s7appo/ELEMENT-camping-platform/images/8607A12A-2D4D-4090-AF0A-3B770DCC6D59.jpg

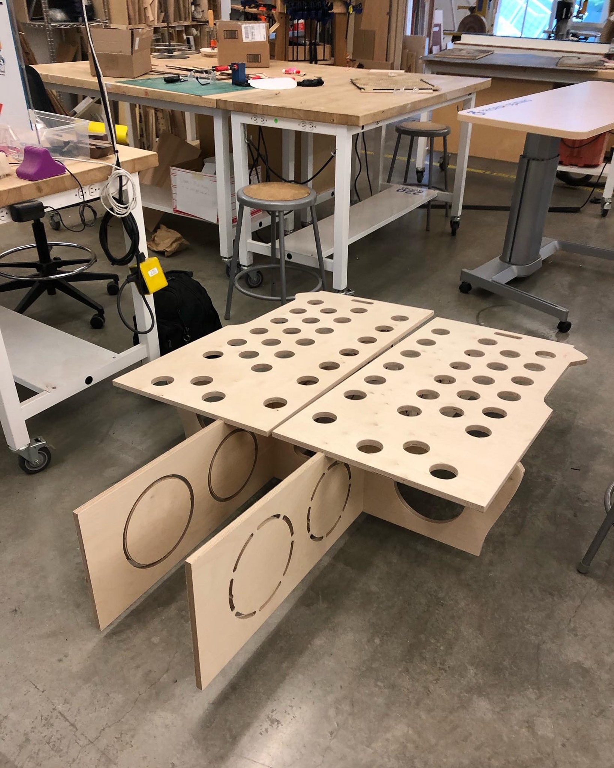
images/8607A12A-2D4D-4090-AF0A-3B770DCC6D59.jpg
