s7appo/ELEMENT-camping-platform/images/IMG_0168.jpg

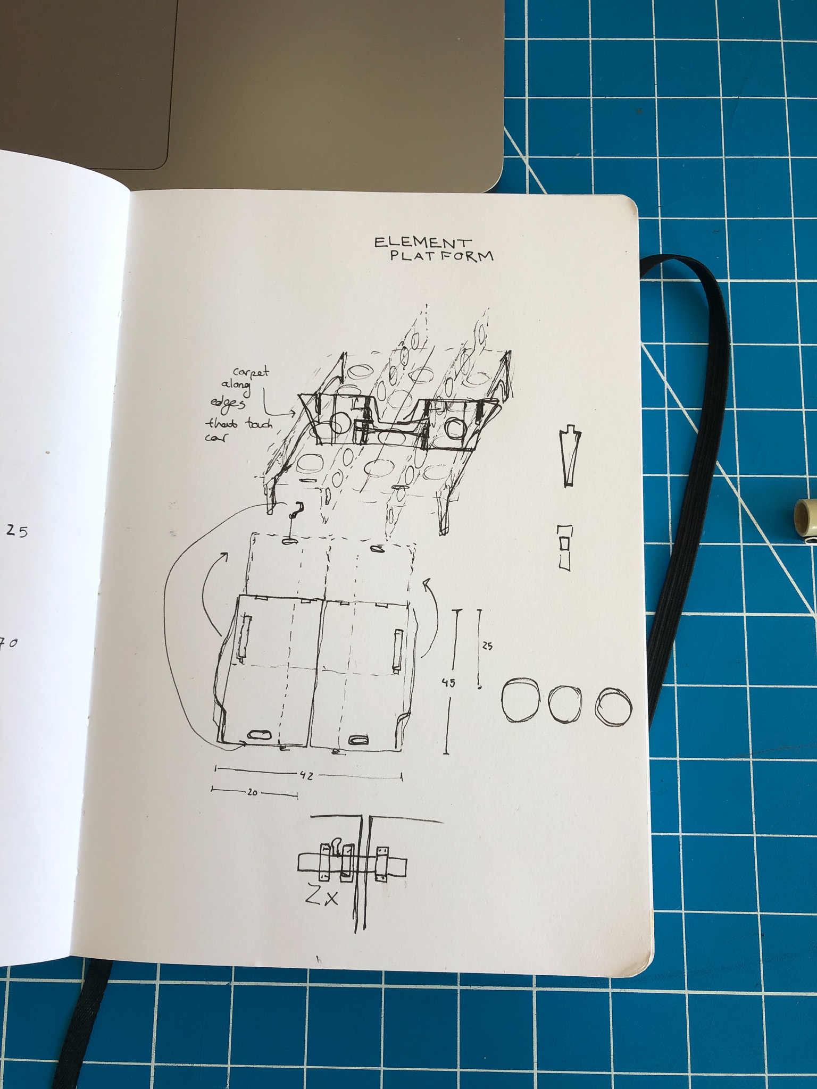
images/IMG_0168.jpg
