s7appo/ELEMENT-camping-platform/images/IMG_0304.jpg

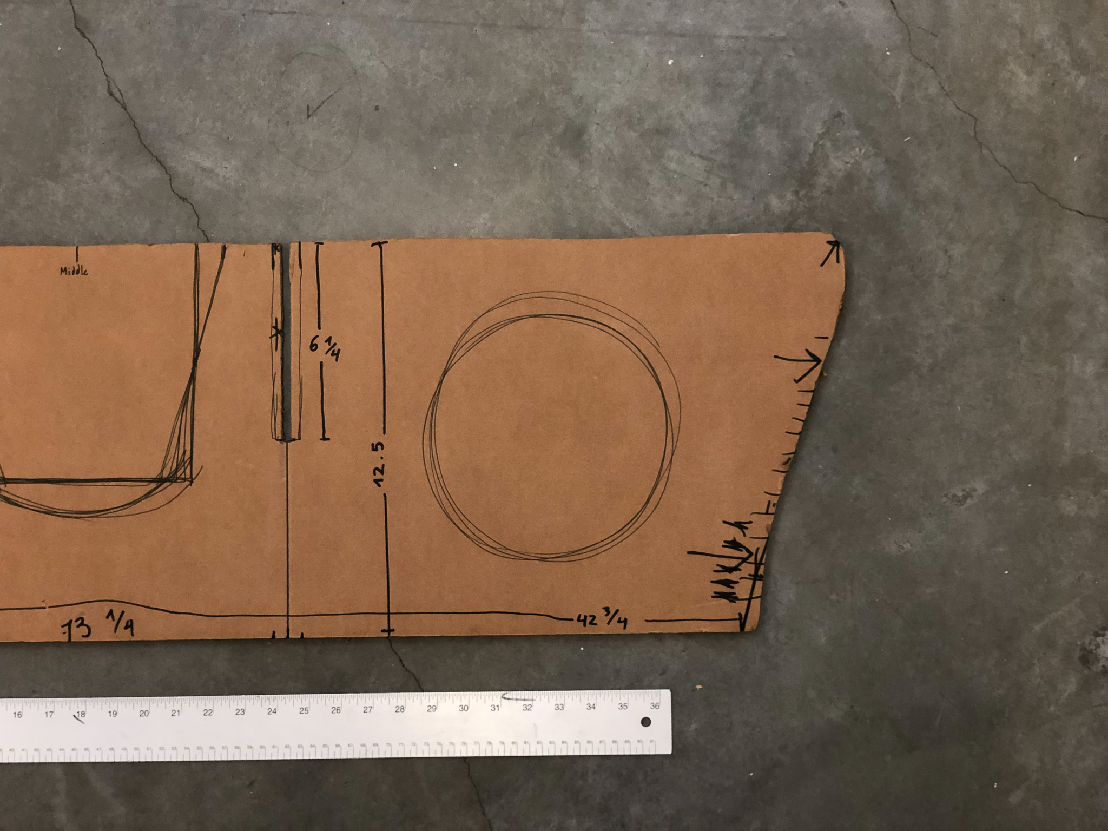
images/IMG_0304.jpg
