s7appo/ELEMENT-camping-platform/images/IMG_1578.jpg

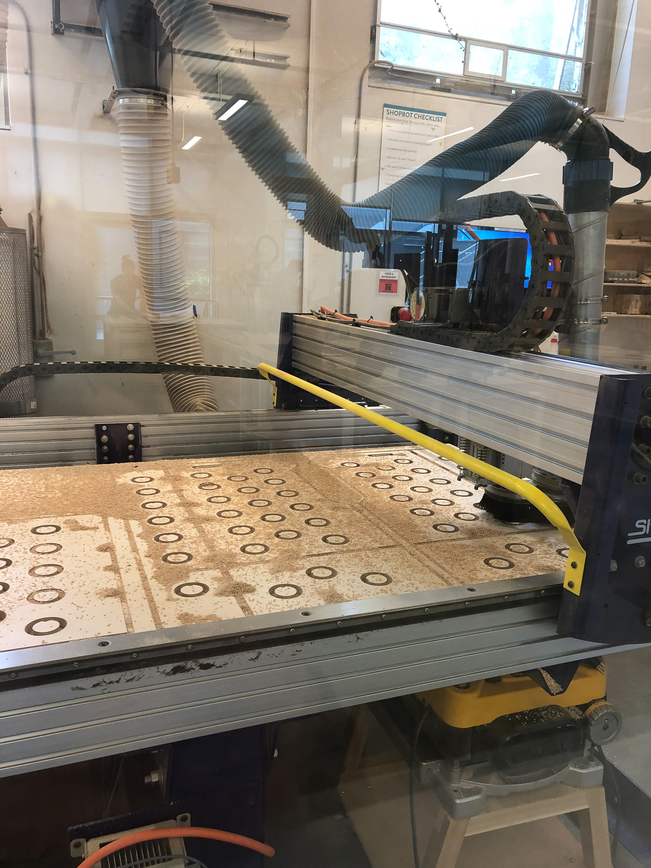
images/IMG_1578.jpg
