s7appo/ELEMENT-camping-platform/images/IMG_1602.jpg

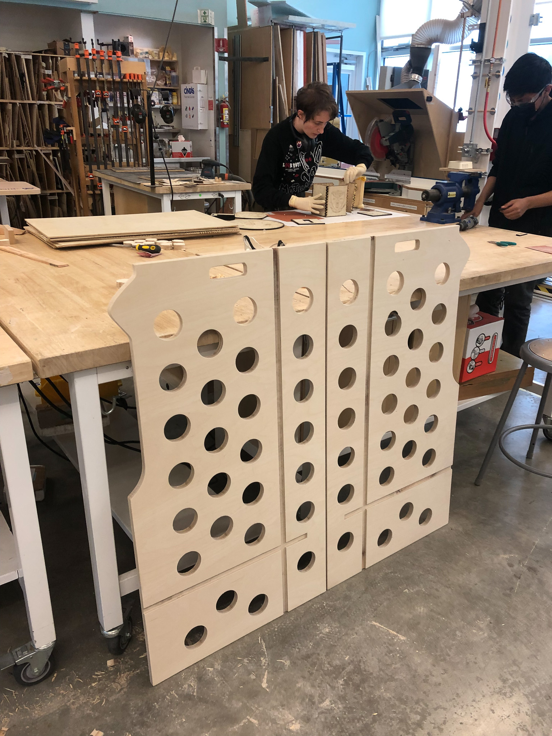
images/IMG_1602.jpg
