s7appo/ELEMENT-camping-platform/images/IMG_1611.jpg

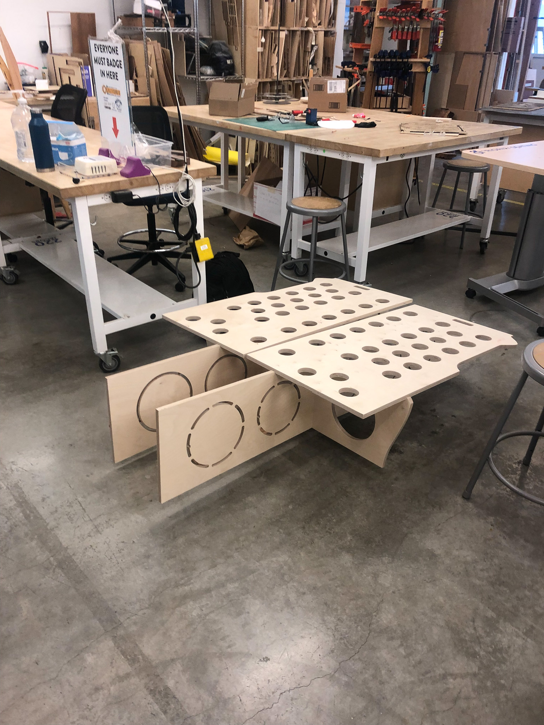
images/IMG_1611.jpg
