s7appo/ELEMENT-camping-platform/images/IMG_1734.jpg

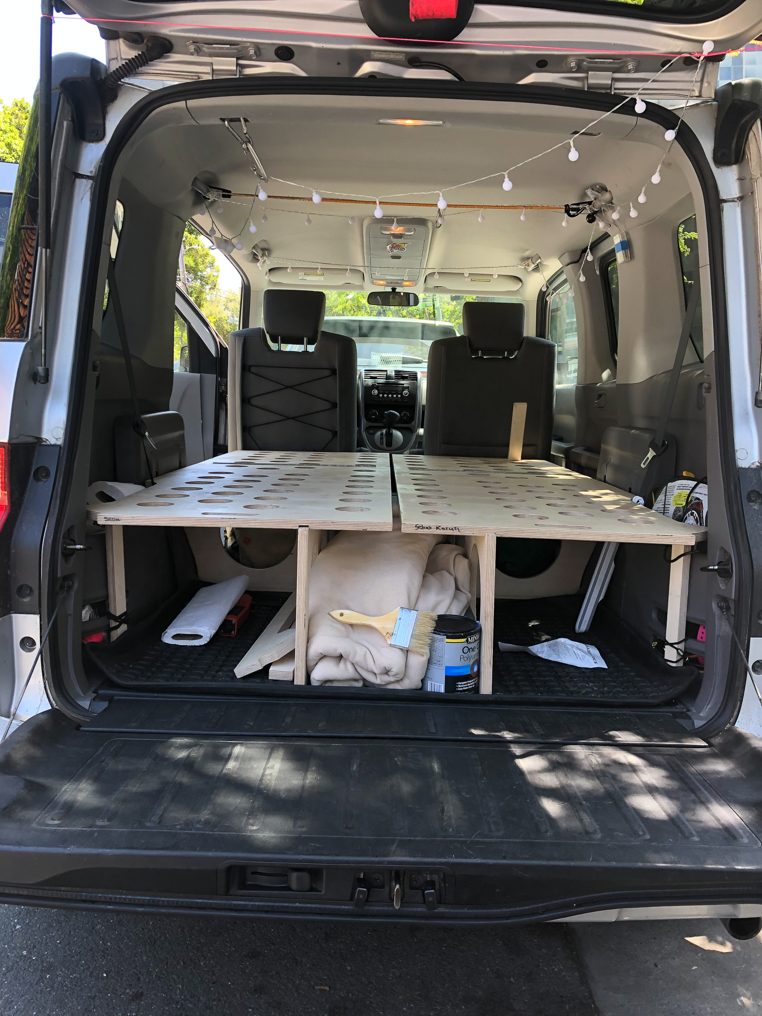
images/IMG_1734.jpg
