s7appo/ELEMENT-camping-platform/images/IMG_1735.jpg

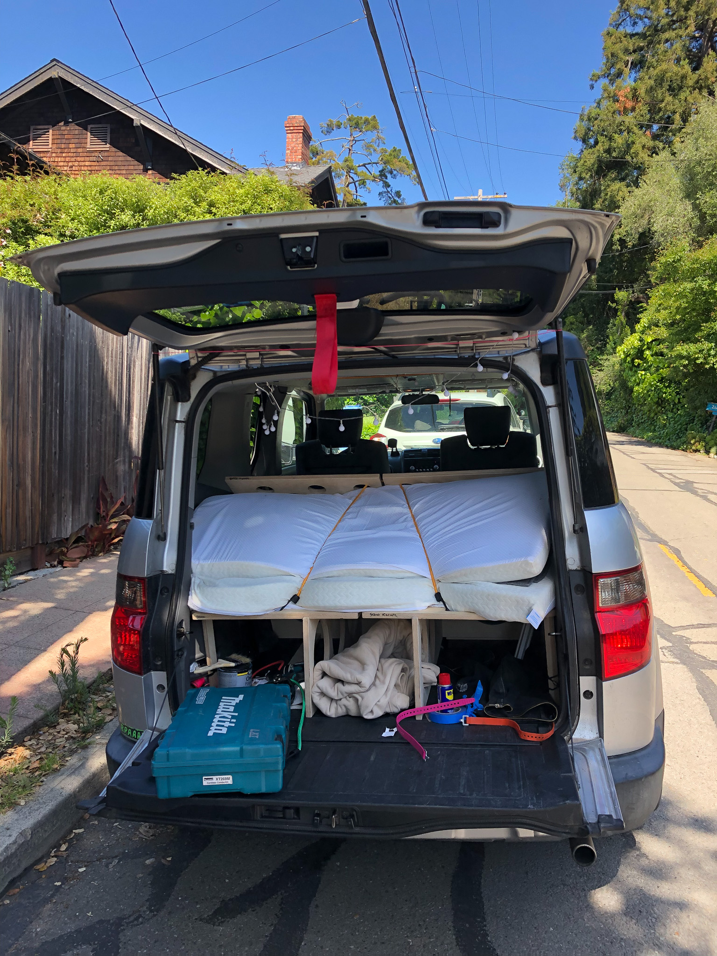
images/IMG_1735.jpg
