s7appo/ELEMENT-camping-platform/images/IMG_1738.jpg

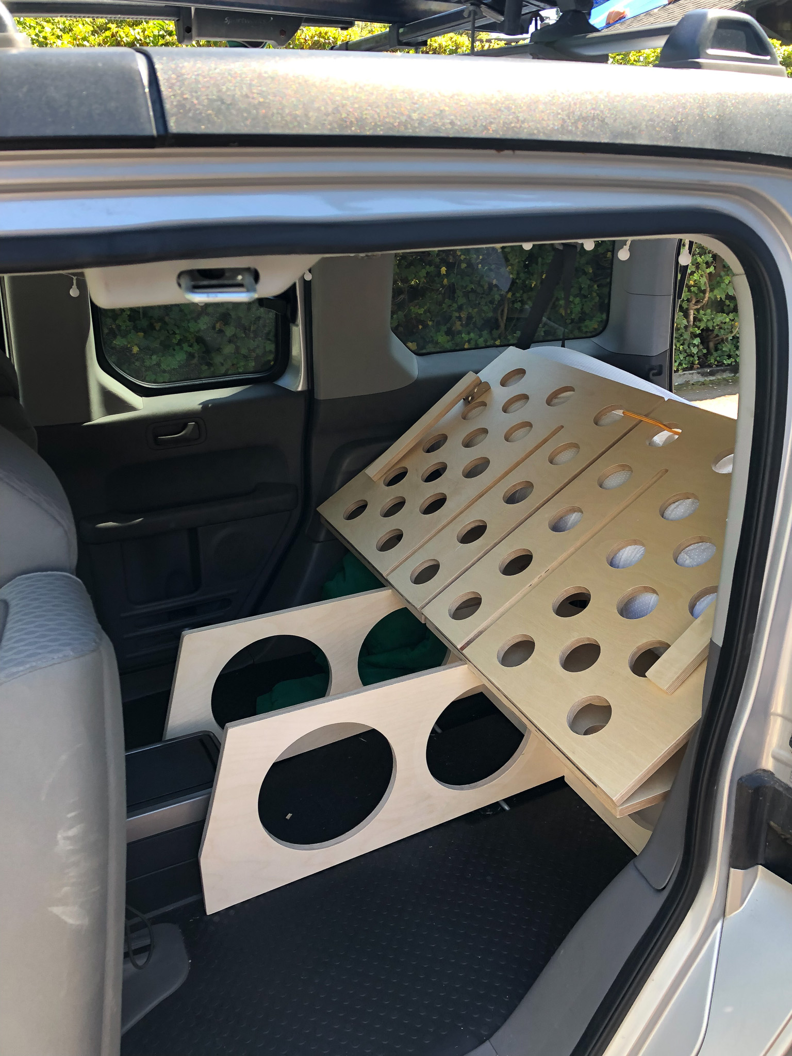
images/IMG_1738.jpg
