s7appo/ELEMENT-camping-platform/images/IMG_1740.jpg

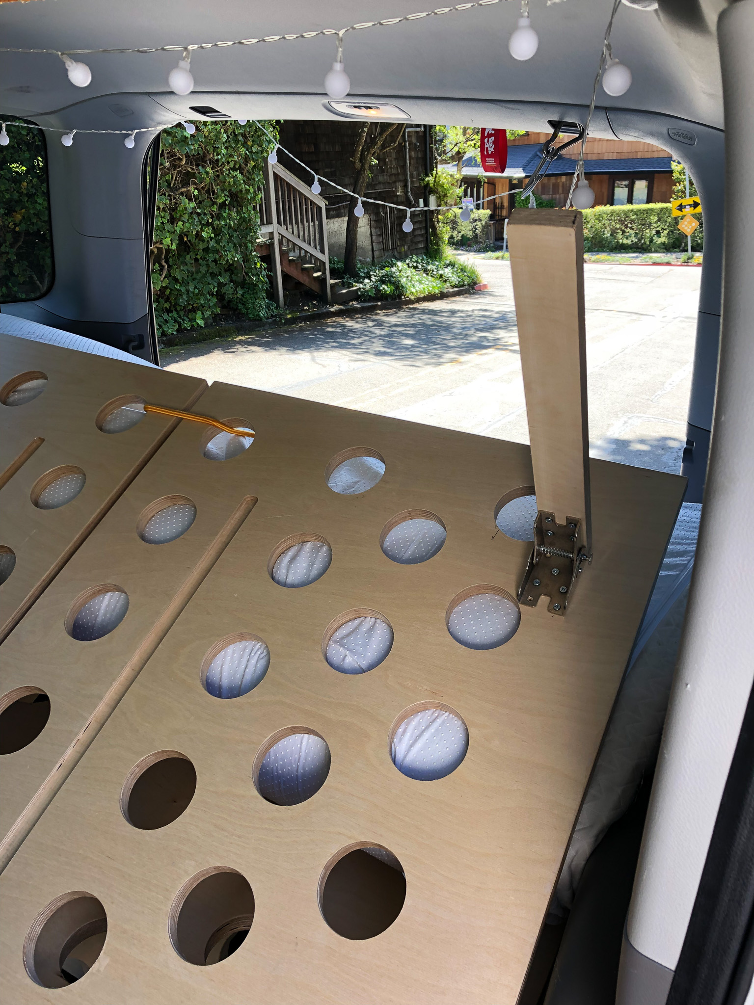
images/IMG_1740.jpg
