s7appo/ELEMENT-camping-platform/images/IMG_1876.jpg

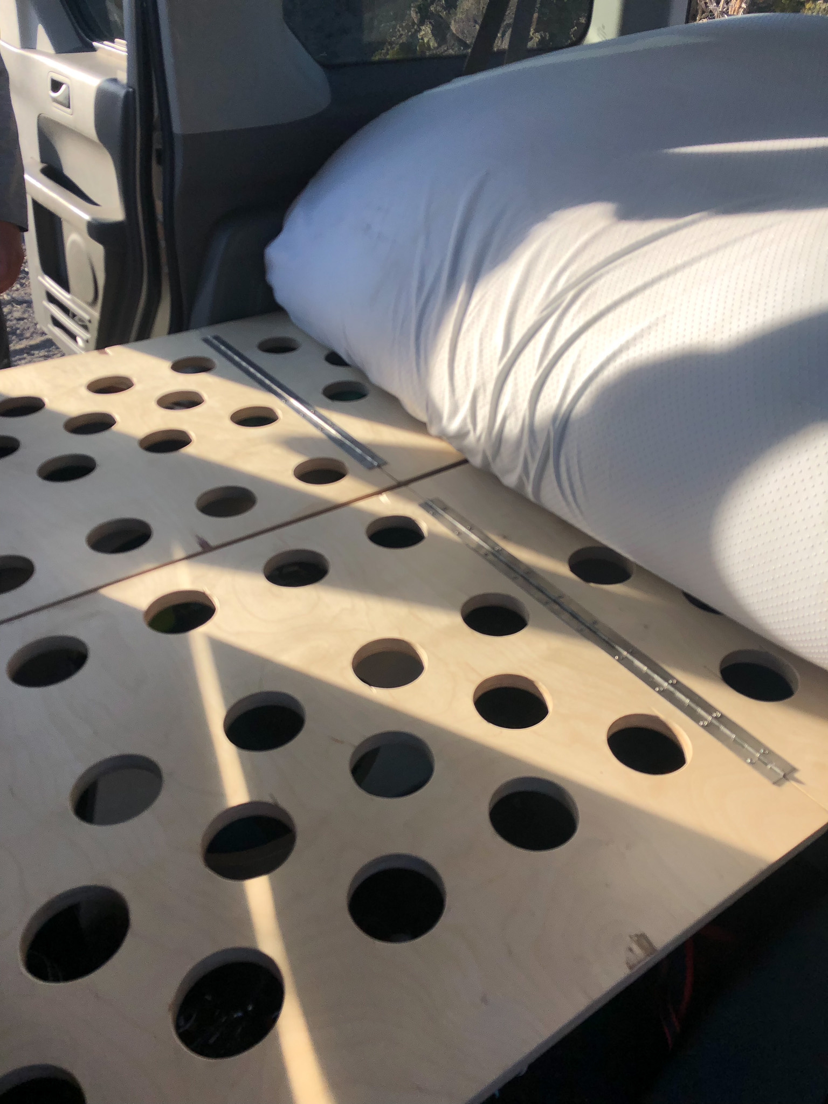
images/IMG_1876.jpg
