s7appo/ELEMENT-camping-platform/images/IMG_1924.jpg

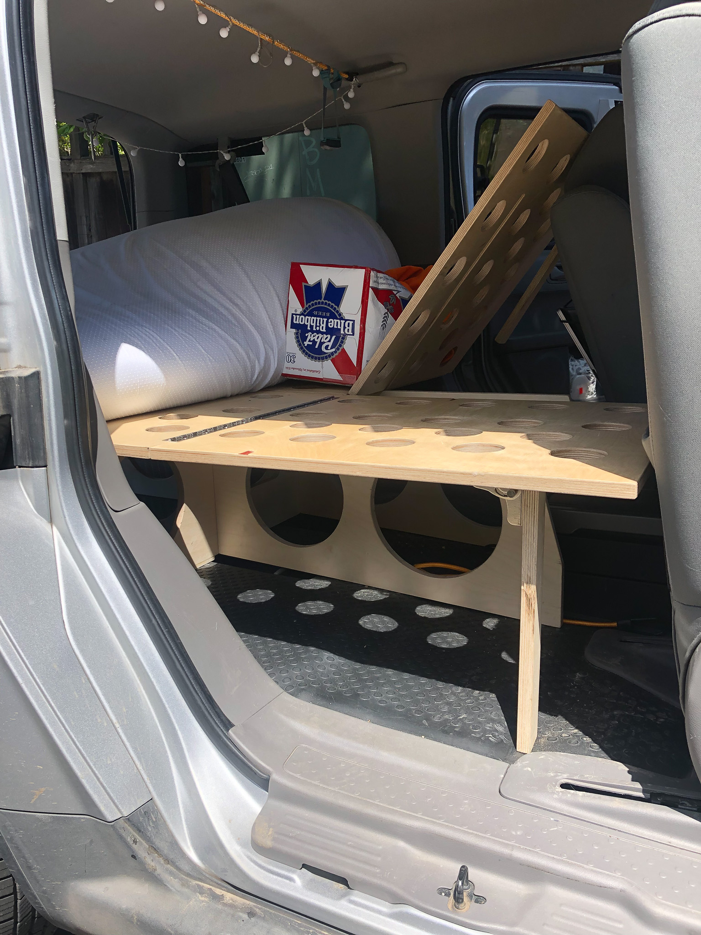
images/IMG_1924.jpg
