s7appo/ELEMENT-camping-platform/images/IMG_7135.jpg

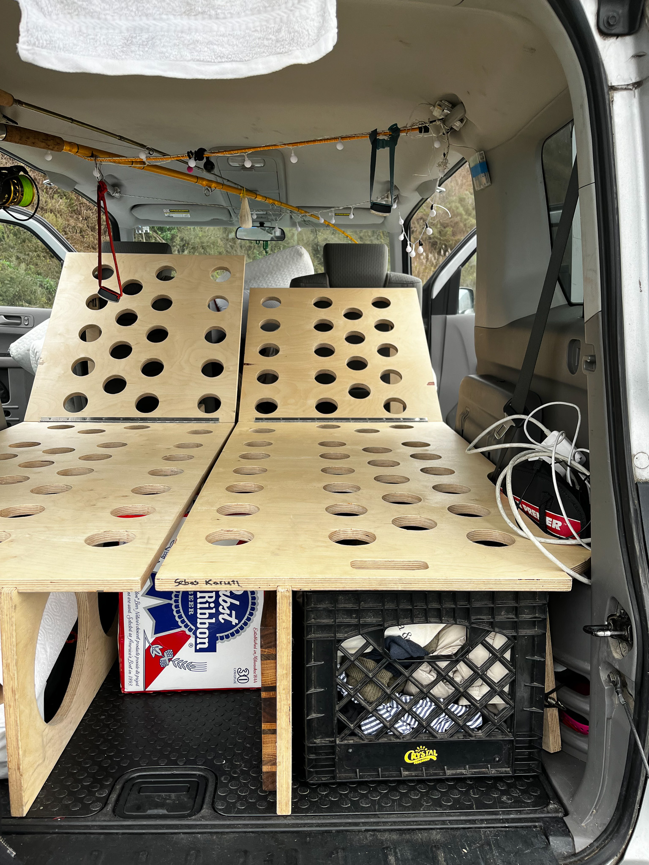
images/IMG_7135.jpg
