s7appo/ELEMENT-camping-platform/images/IMG_7140.jpg

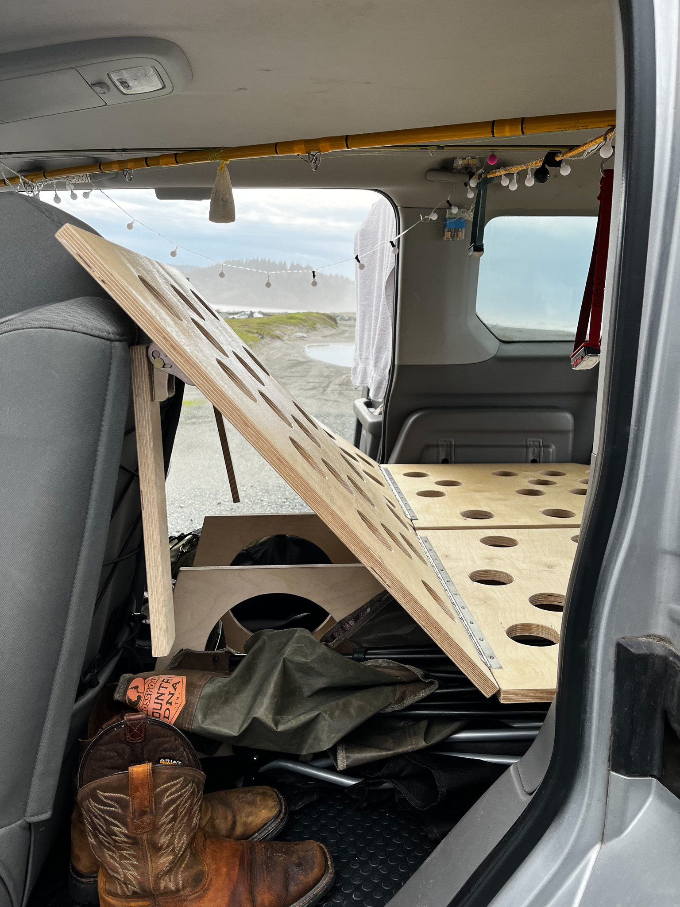
images/IMG_7140.jpg
