s7appo/ELEMENT-camping-platform/images/IMG_7141.jpg

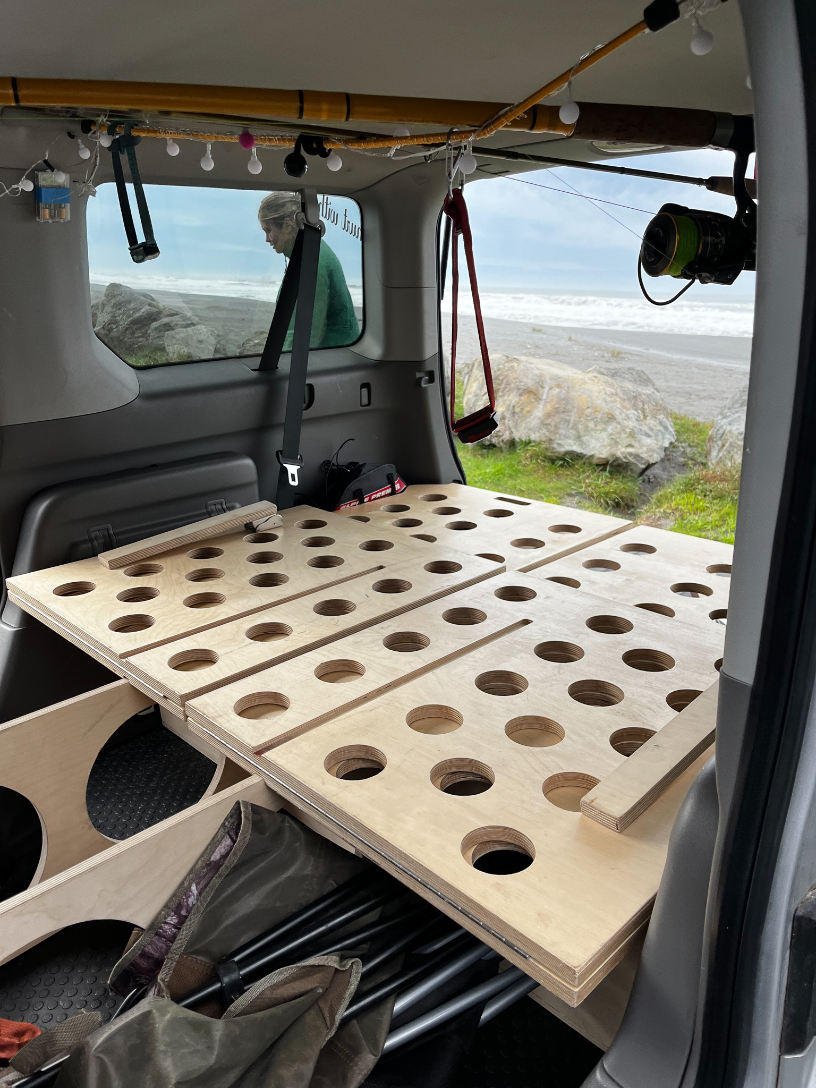
images/IMG_7141.jpg
