s7appo/ELEMENT-camping-platform/images/IMG_7143.jpg

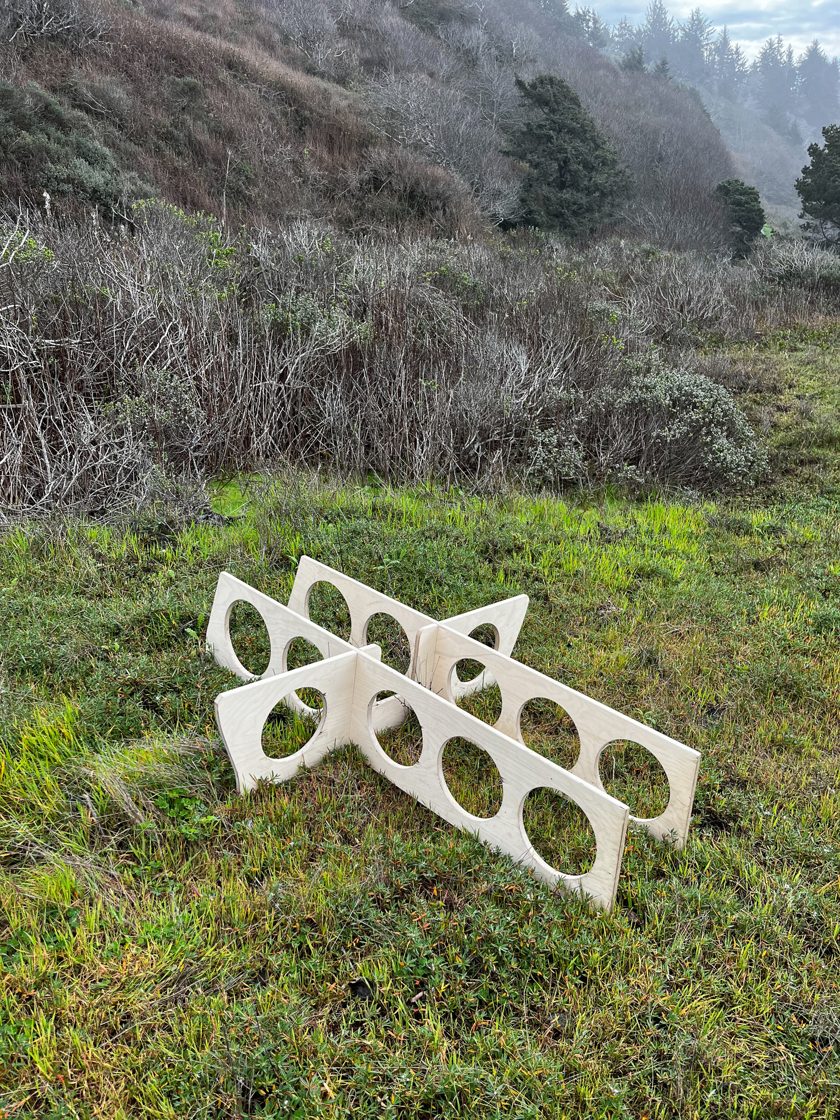
images/IMG_7143.jpg
