s7appo/ELEMENT-camping-platform/images/IMG_7145.jpg

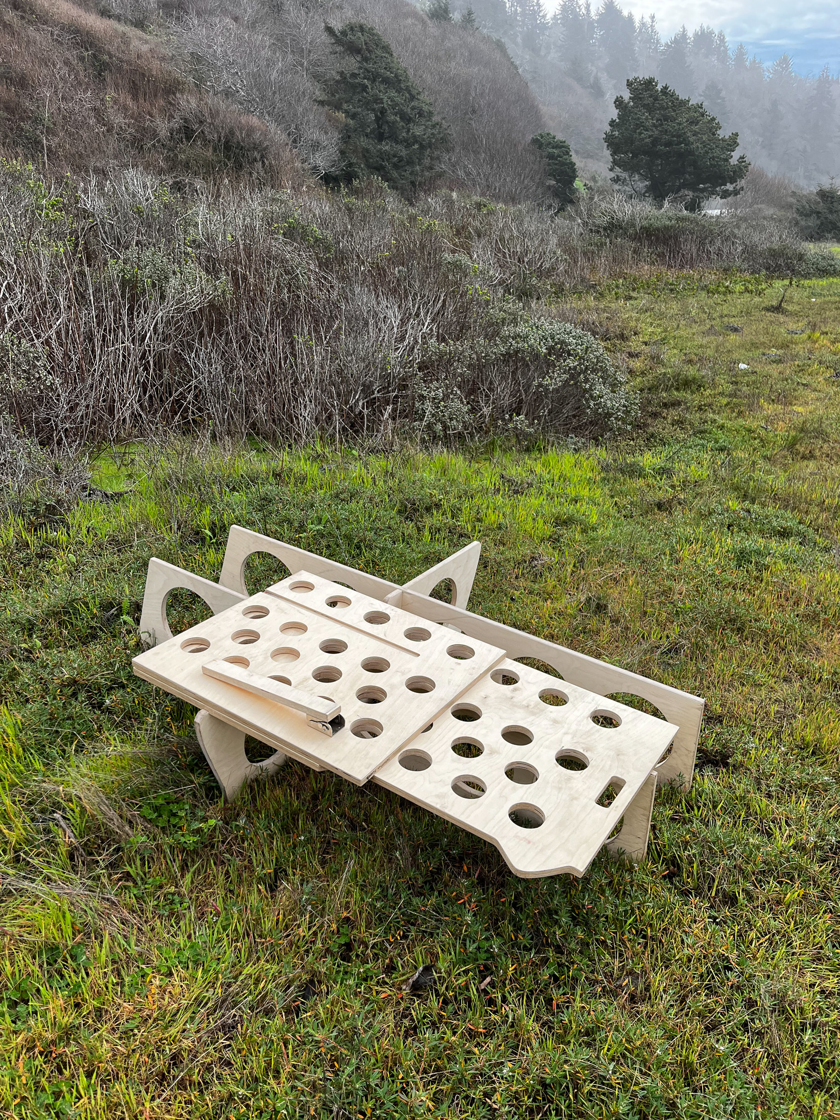
images/IMG_7145.jpg
