s7appo/ELEMENT-camping-platform/images/IMG_7146.jpg

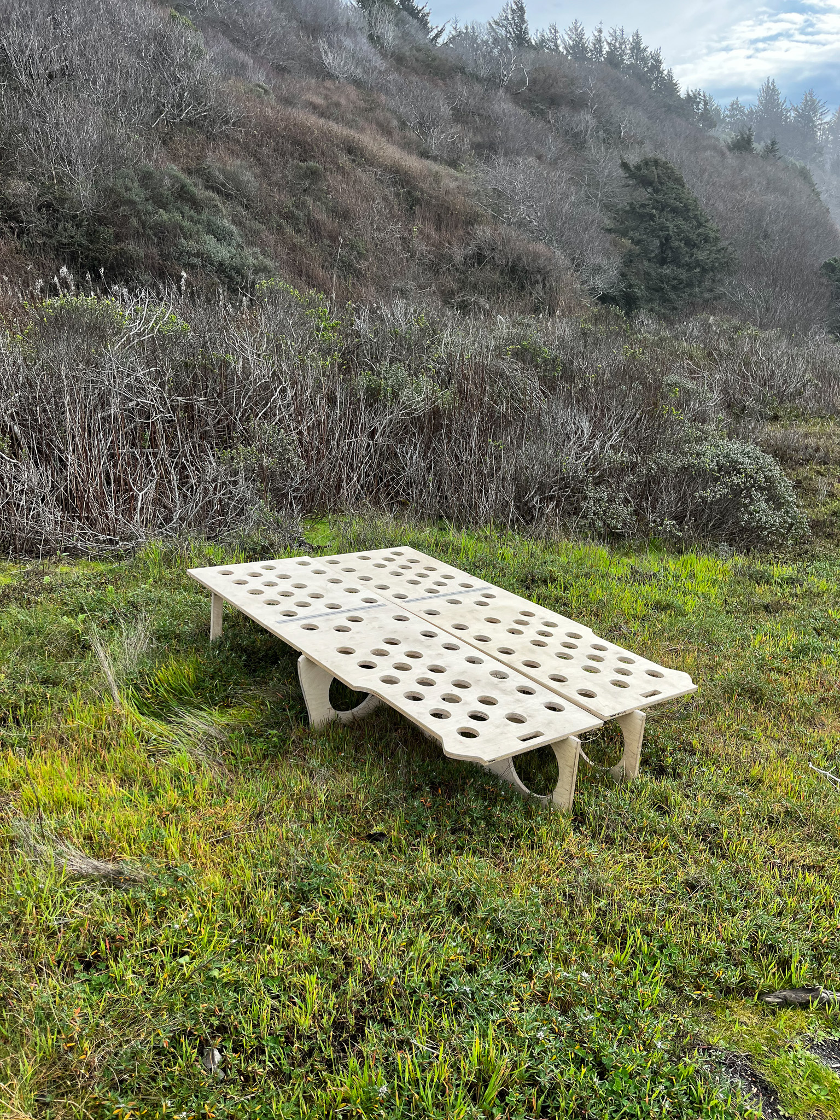
images/IMG_7146.jpg
