s7appo/ELEMENT-camping-platform/images/IMG_7158.jpg

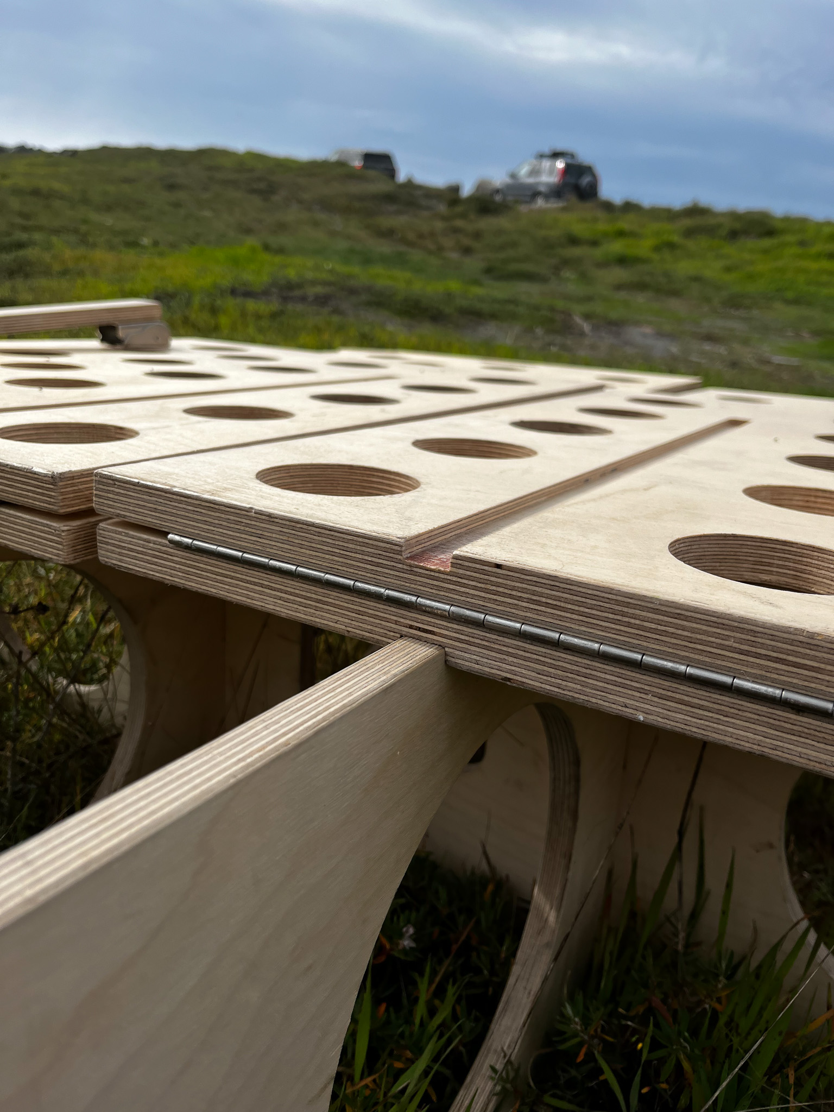
images/IMG_7158.jpg
