s7appo/ELEMENT-camping-platform/images/IMG_7159.jpg

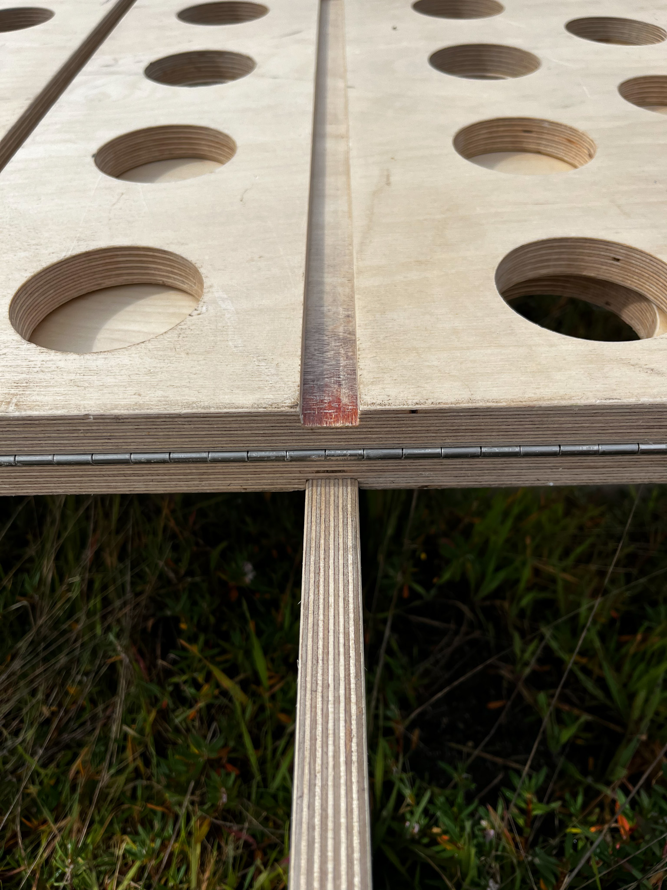
images/IMG_7159.jpg
