s7appo/ELEMENT-camping-platform/images/IMG_7160.jpg

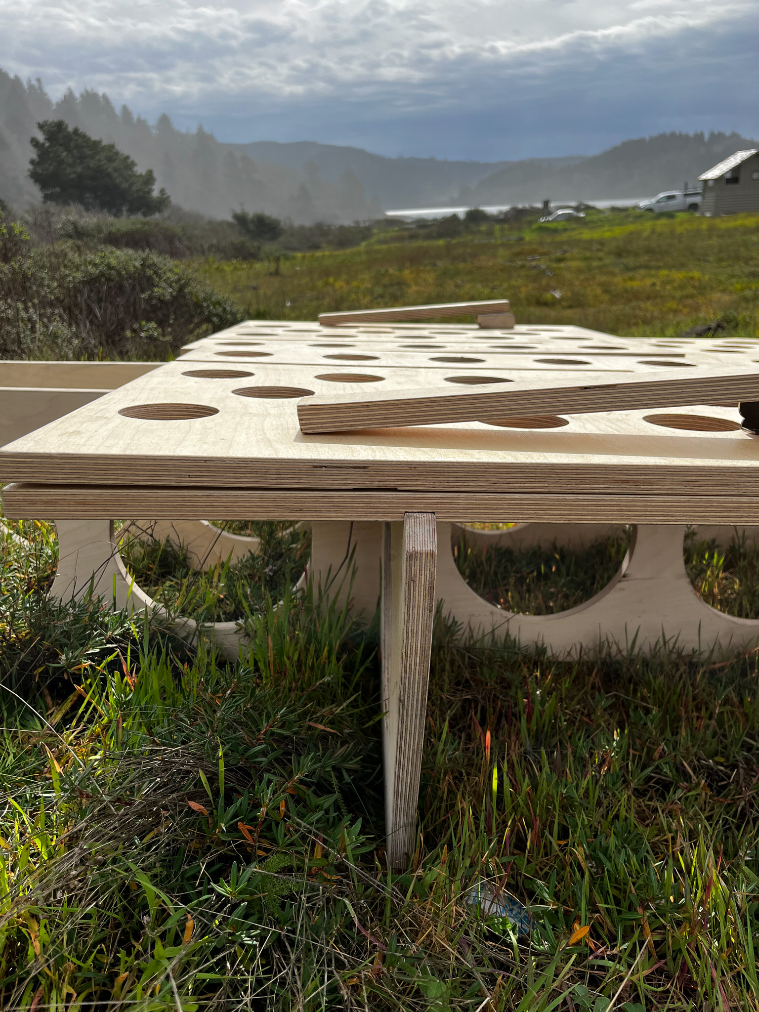
images/IMG_7160.jpg
