s7appo/ELEMENT-camping-platform/images/IMG_7232.jpg

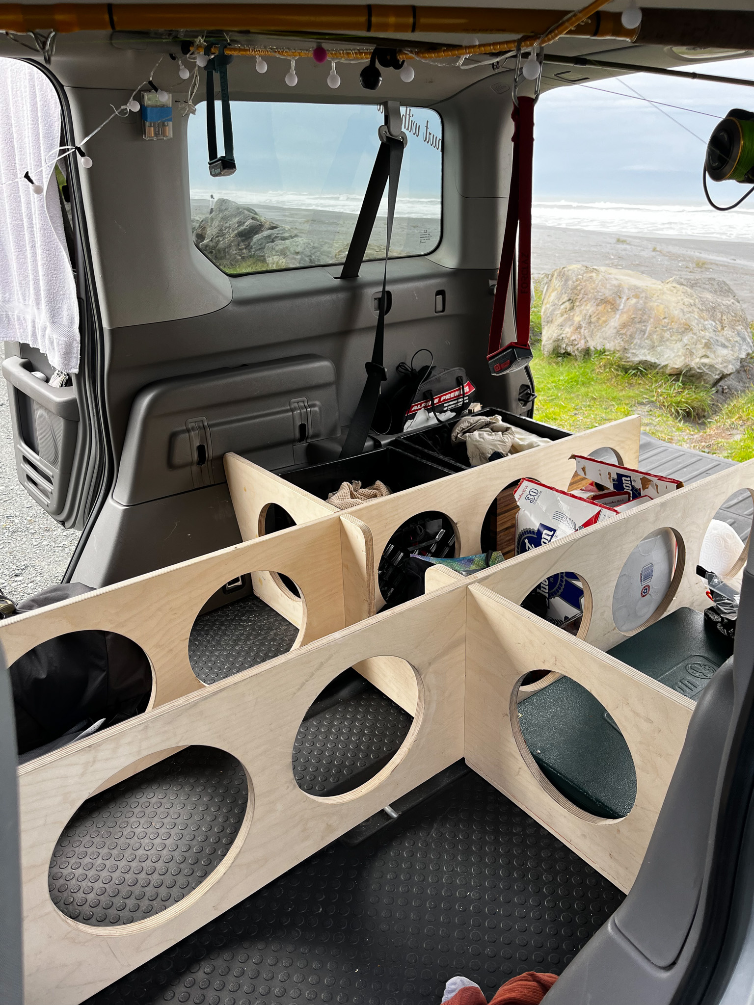
images/IMG_7232.jpg
