s7appo/ELEMENT-camping-platform/images/IMG_7234.jpg

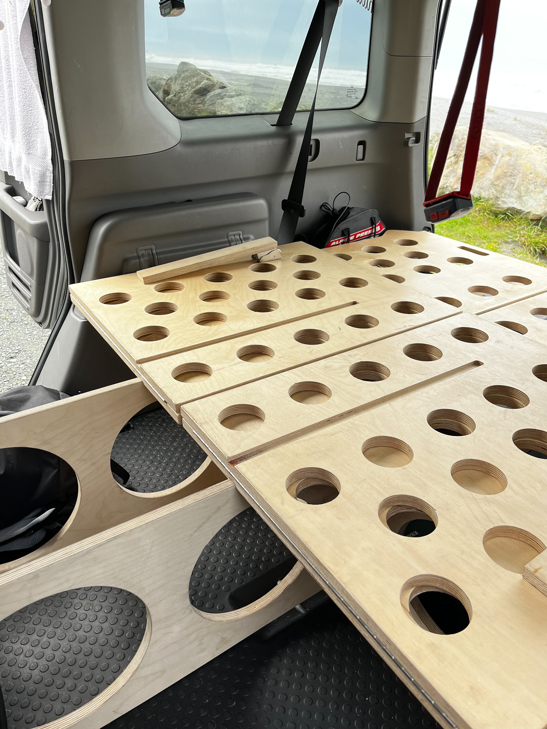
images/IMG_7234.jpg
